sparkfun/SparkFun_RTK_EVK/docs/assets/board_files/dimensions.png

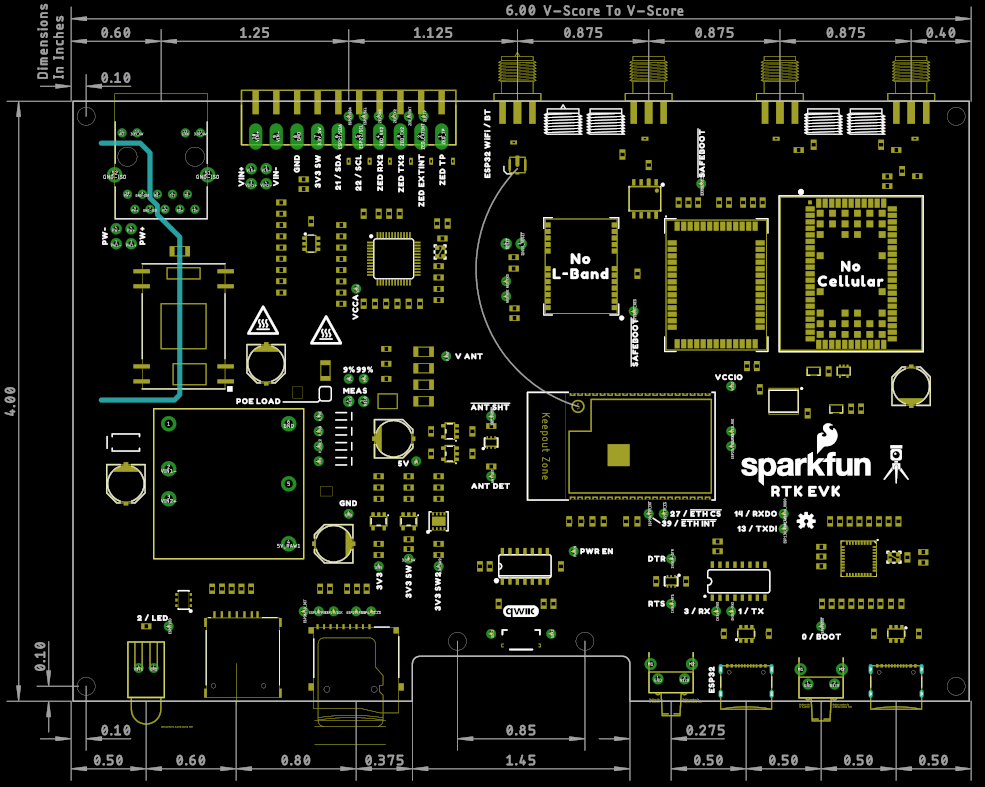
docs/assets/board_files/dimensions.png
