sparkfun/SparkFun_RTK_EVK/docs/assets/board_files/SparkFun_RTK_EVK-Back.png

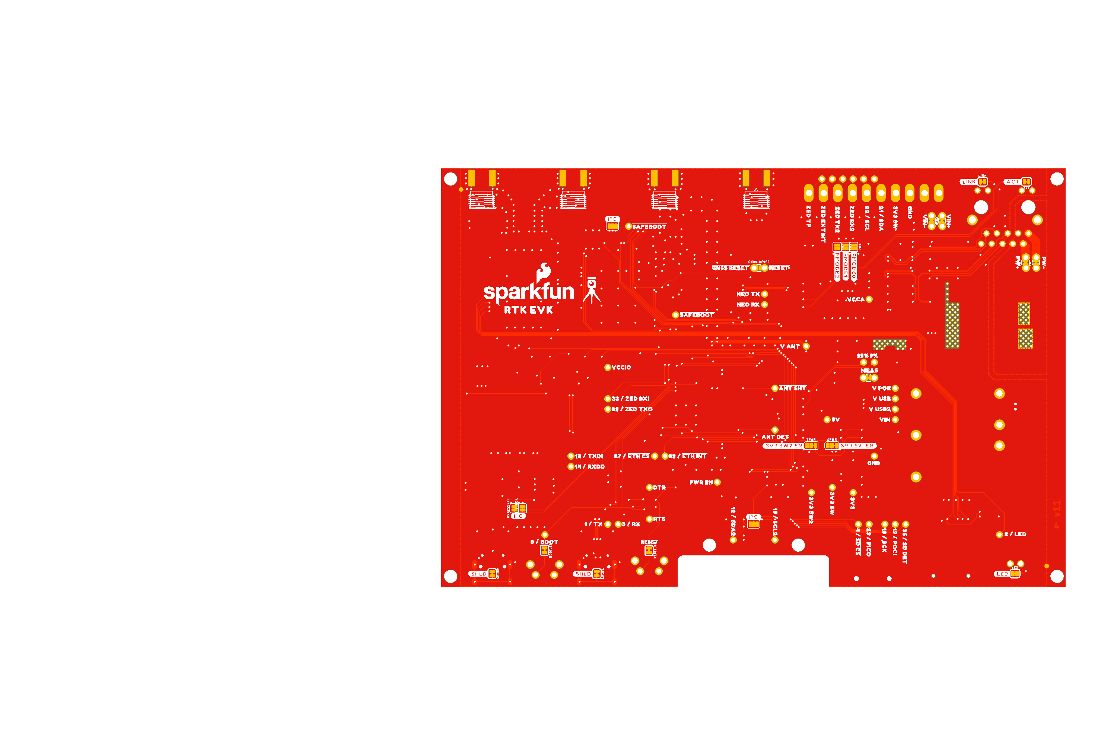
docs/assets/board_files/SparkFun_RTK_EVK-Back.png
