sparkfun/SparkFun_RTK_EVK/docs/assets/board_files/SparkFun_RTK_EVK.png

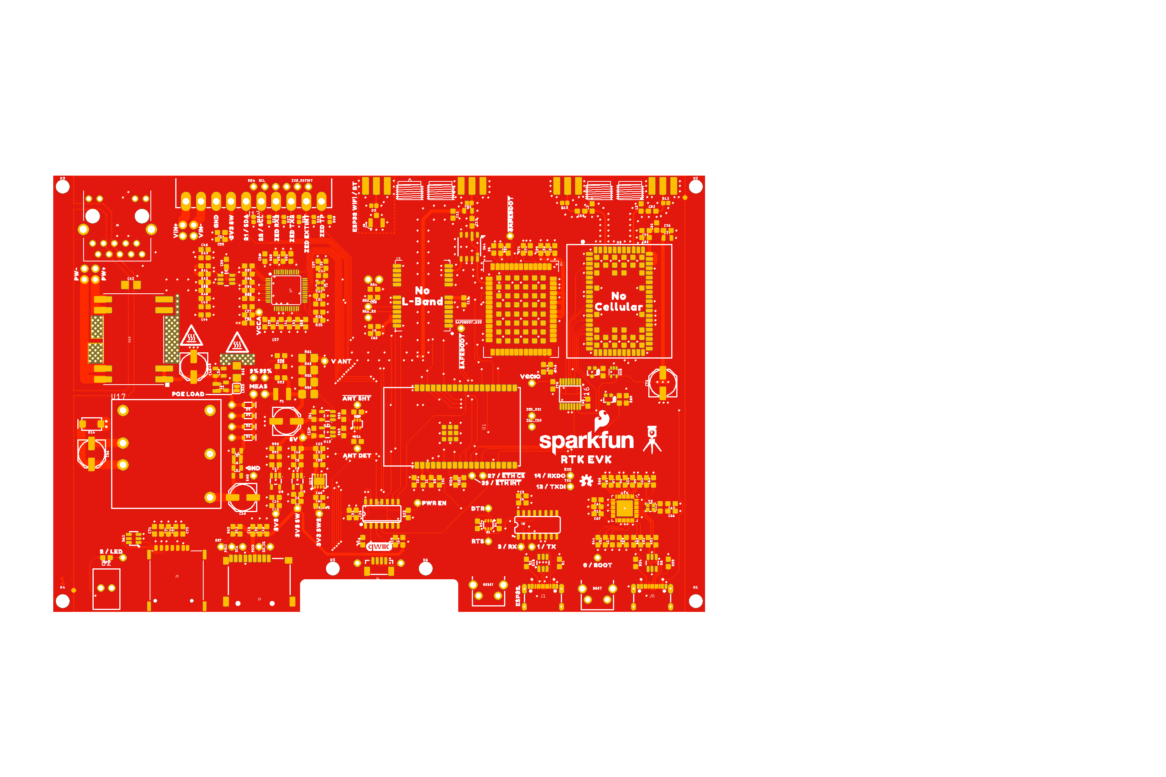
docs/assets/board_files/SparkFun_RTK_EVK.png
