sparkfun/SparkFun_RTK_EVK/docs/assets/img/24342-RTK-EVK-Feature.jpg

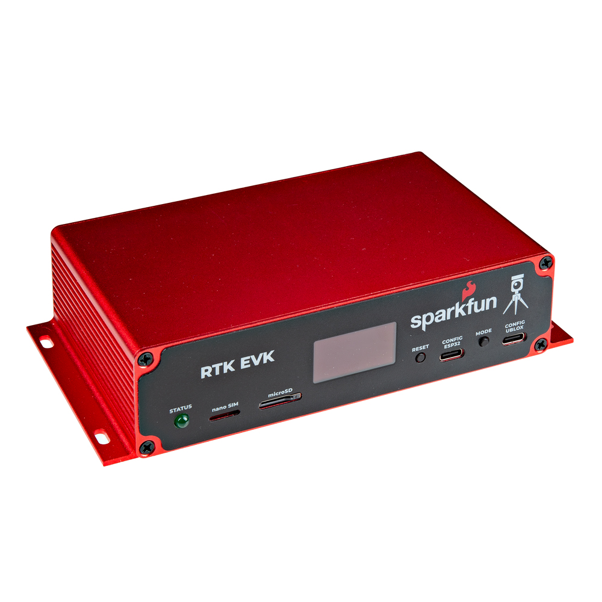
docs/assets/img/24342-RTK-EVK-Feature.jpg
