sparkfun/SparkFun_RTK_EVK/docs/assets/img/PCB.png

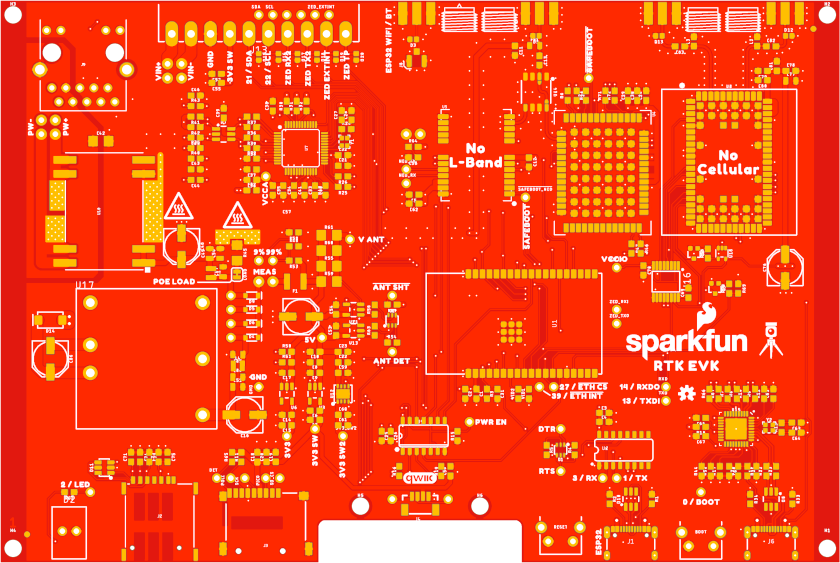
docs/assets/img/PCB.png
