sparkfun/SparkFun_RTK_EVK/docs/assets/RTK_EVK_Enclosure/Rear_Panel/RTK_EVK_Rear_Panel.pdf

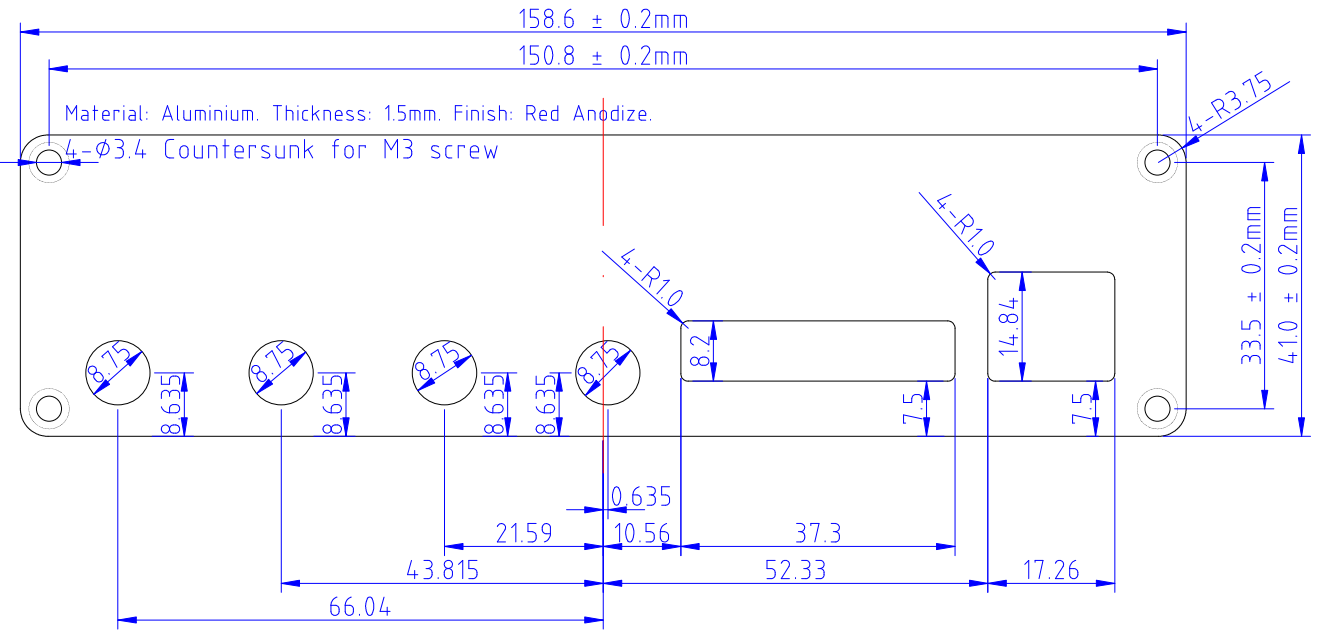
[picture p86: page 1]
