sparkfun/SparkFun_RTK_EVK/docs/assets/RTK_EVK_Enclosure/Rear_Sticker/RTK_EVK_Rear_Sticker_Dimensions.pdf

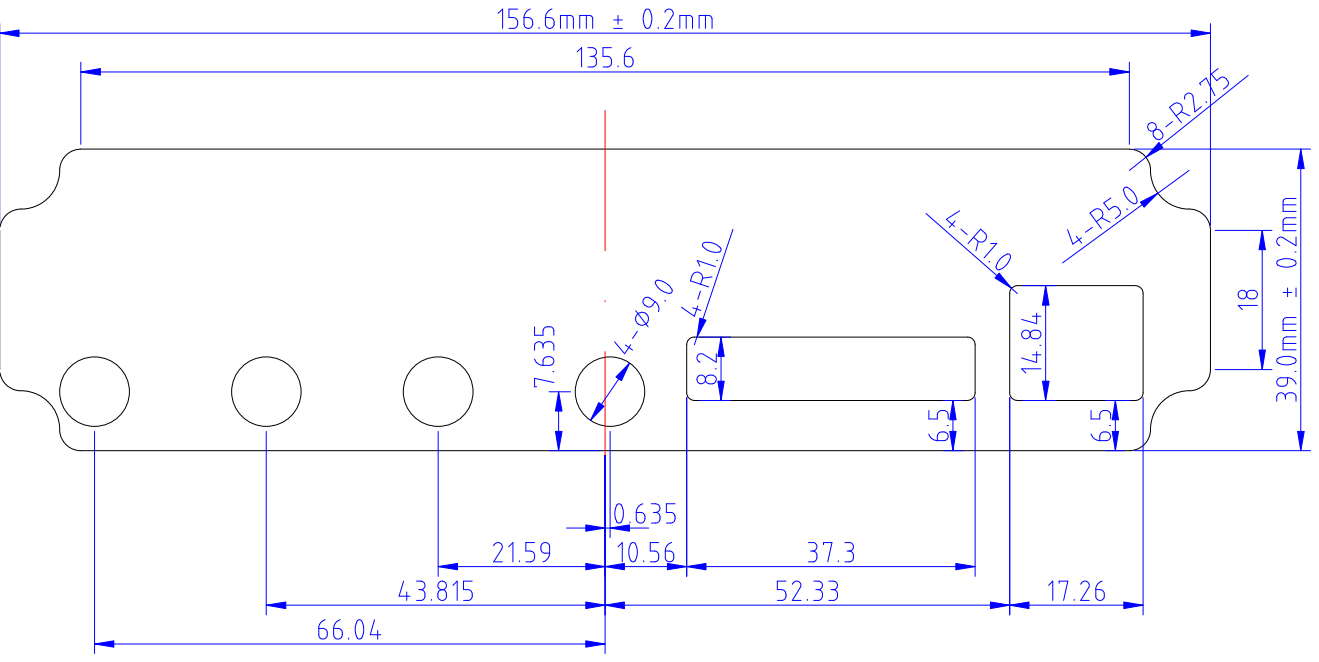
[picture p87: page 1]
