sparkfun/SparkFun_RTK_EVK/docs/assets/RTK_EVK_Enclosure/Front_Panel/RTK_EVK_Front_Panel.pdf

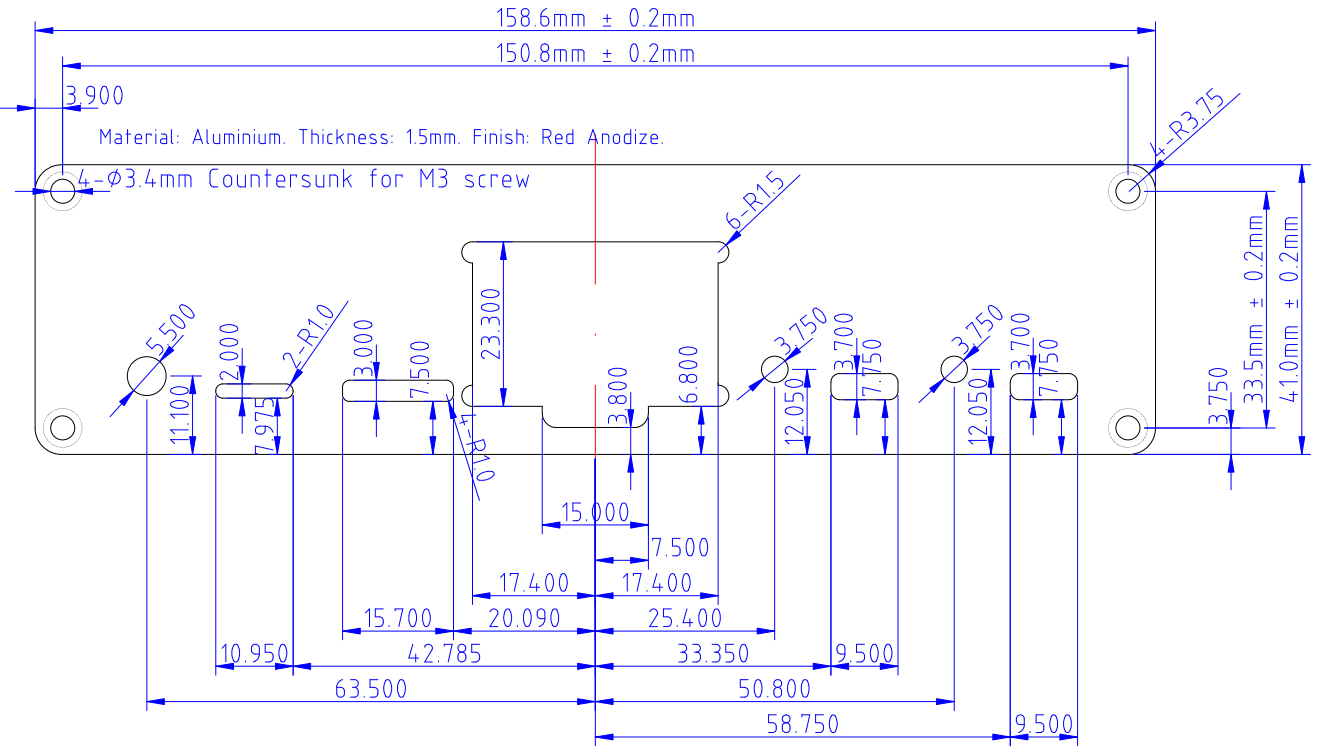
[picture p88: page 1]
