sparkfun/SparkFun_RTK_EVK/Example_Sketches/6_2_LBand_Corrections_with_NEO-D9S/6_2_LBand_Corrections_with_NEO-D9S.ino

/*
  SparkFun RTK EVK Test Sketch

  License: MIT. Please see LICENSE.md for more details

  This example shows how to receive u-blox PointPerfect L-Band correction data
  with the NEO-D9S and transfer it to the ZED-F9P over UART or I2C.

  The L-Band SPARTN correction data is encrypted; the ZED-F9P requires keys to decrypt it.
  Update secrets.h with your PointPerfect L-Band keys from Thingstream.

  ESP32-WROVER-IE Pin Allocations:
  D0  : Boot + Boot Button
  D1  : Serial TX (CH340 RX)
  D2  : STAT LED
  D3  : Serial RX (CH340 TX)
  D4  : SD CS
  D5  : GNSS Time Pulse - via 74HC4066 switch and PWREN
  D12 : SDA2 - Qwiic OLED - via 74HC4066 switch and PWREN
  D13 : Serial1 TX - LARA_TXDI
  D14 : Serial1 RX - LARA RXDO
  D15 : SCL2 - Qwiic OLED - via 74HC4066 switch and PWREN
  D16 : N/A
  D17 : N/A
  D18 : SPI SCK
  D19 : SPI POCI
  D21 : I2C SDA
  D22 : I2C SCL
  D23 : SPI PICO
  D25 : Serial2 RX - ZED-F9P TXO
  D26 : LARA Power On
  D27 : Ethernet Chip Select
  D32 : PWREN
  D33 : Serial2 TX - ZED-F9P RXI
  A34 : LARA Network Indicator
  A35 : Board Detect (3.0V)
  A36 : SD Card Detect
  A39 : Ethernet Interrupt
*/

#define noPush // Uncomment this line to disable pushing the correction data over I2C

#include "secrets.h" // <- Copy and paste the Current Key and Next Key into secrets.h

#include <Wire.h> // Needed for I2C to GNSS
TwoWire I2C_1 = TwoWire(0);

#include <SparkFun_u-blox_GNSS_v3.h> //http://librarymanager/All#SparkFun_u-blox_GNSS_v3
SFE_UBLOX_GNSS myGNSS; // ZED-F9x
SFE_UBLOX_GNSS myLBand; // NEO-D9S

const uint32_t myLBandFreq = 1556290000; // Uncomment this line to use the US SPARTN 1.8 service
//const uint32_t myLBandFreq = 1545260000; // Uncomment this line to use the EU SPARTN 1.8 service

#define OK(ok) (ok ? F("  ->  OK") : F("  ->  ERROR!")) // Convert uint8_t into OK/ERROR

const int STAT_LED = 2;
const int SD_CS = 4; // Chip select for the microSD card
const int GNSS_INT = 5; // ZED_F9P time pulse interrupt
const int SDA_2 = 12; // OLED
const int SERIAL1_TX = 13; // LARA_TXDI
const int SERIAL1_RX = 14; // LARA RXDO
const int SCL_2 = 15; // OLED
const int SDA_1 = 21; // ZED-F9P and NEO-D9S
const int SCL_1 = 22; // ZED-F9P and NEO-D9S
const int SERIAL2_RX = 25; // ZED-F9P TXO
const int LARA_PWR = 26; // LARA_PWR_ON - inverted - set LARA_PWR high to pull LARA_PWR_ON low
const int ETHERNET_CS = 27; // Chip select for the WizNet W5500
const int PWREN = 32; // 74HC4066 switch Enable - pull high to enable SCL2/SDA2 and GNSS_INT
const int SERIAL2_TX = 33; // ZED-F9P RXI
const int LARA_NI = 34; // LARA Network Indicator - only valid when the LARA is powered on
const int SD_PRESENT = 36; // microSD card card present - from the microSD socket switch
const int ETHERNET_INT = 39; // WizNet W5500 interrupt

//=-=-=-=-=-=-=-=-=-=-=-=-=-=-=-=-=-=-=-=-=-=-=-=-=-=-=-=-=-=-=-=-=-=-=-=-=-=-=-=-=-=-=-=-=

// Callback: pushRXMPMP will be called when new PMP data arrives
// See u-blox_structs.h for the full definition of UBX_RXM_PMP_message_data_t
//         _____  You can use any name you like for the callback. Use the same name when you call setRXMPMPmessageCallbackPtr
//        /               _____  This _must_ be UBX_RXM_PMP_message_data_t
//        |              /              _____ You can use any name you like for the struct
//        |              |             /
//        |              |             |
void pushRXMPMP(UBX_RXM_PMP_message_data_t *pmpData)
{
  //Extract the raw message payload length
  uint16_t payloadLen = ((uint16_t)pmpData->lengthMSB << 8) | (uint16_t)pmpData->lengthLSB;
  Serial.print(F("New RXM-PMP data received. Message payload length is "));
  Serial.print(payloadLen);

#ifndef noPush

  Serial.println(F(" Bytes. Pushing it to the GNSS..."));
  
  //Push the PMP data to the GNSS
  //The payload length could be variable, so we need to push the header and payload, then checksum
  myGNSS.pushRawData(&pmpData->sync1, (size_t)payloadLen + 6); // Push the sync chars, class, ID, length and payload
  myGNSS.pushRawData(&pmpData->checksumA, (size_t)2); // Push the checksum bytes

#else

  Serial.println(F(" Bytes."));

#endif

}

//=-=-=-=-=-=-=-=-=-=-=-=-=-=-=-=-=-=-=-=-=-=-=-=-=-=-=-=-=-=-=-=-=-=-=-=-=-=-=-=-=-=-=-=-=

// Callback: printPVTdata will be called when new NAV PVT data arrives
// See u-blox_structs.h for the full definition of UBX_NAV_PVT_data_t
//         _____  You can use any name you like for the callback. Use the same name when you call setAutoPVTcallbackPtr
//        /                  _____  This _must_ be UBX_NAV_PVT_data_t
//        |                 /               _____ You can use any name you like for the struct
//        |                 |              /
//        |                 |              |
void printPVTdata(UBX_NAV_PVT_data_t *ubxDataStruct)
{
  double latitude = ubxDataStruct->lat; // Print the latitude
  Serial.print(F("Lat: "));
  Serial.print(latitude / 10000000.0, 7);

  double longitude = ubxDataStruct->lon; // Print the longitude
  Serial.print(F("  Long: "));
  Serial.print(longitude / 10000000.0, 7);

  double altitude = ubxDataStruct->hMSL; // Print the height above mean sea level
  Serial.print(F("  Height: "));
  Serial.print(altitude / 1000.0, 3);

  uint8_t fixType = ubxDataStruct->fixType; // Print the fix type
  Serial.print(F("  Fix: "));
  Serial.print(fixType);
  if (fixType == 0)
    Serial.print(F(" (None)"));
  else if (fixType == 1)
    Serial.print(F(" (Dead Reckoning)"));
  else if (fixType == 2)
    Serial.print(F(" (2D)"));
  else if (fixType == 3)
    Serial.print(F(" (3D)"));
  else if (fixType == 3)
    Serial.print(F(" (GNSS + Dead Reckoning)"));
  else if (fixType == 5)
    Serial.print(F(" (Time Only)"));
  else
    Serial.print(F(" (UNKNOWN)"));

  uint8_t carrSoln = ubxDataStruct->flags.bits.carrSoln; // Print the carrier solution
  Serial.print(F("  Carrier Solution: "));
  Serial.print(carrSoln);
  if (carrSoln == 0)
    Serial.print(F(" (None)"));
  else if (carrSoln == 1)
    Serial.print(F(" (Floating)"));
  else if (carrSoln == 2)
    Serial.print(F(" (Fixed)"));
  else
    Serial.print(F(" (UNKNOWN)"));

  uint32_t hAcc = ubxDataStruct->hAcc; // Print the horizontal accuracy estimate
  Serial.print(F("  Horizontal Accuracy Estimate: "));
  Serial.print(hAcc);
  Serial.print(F(" (mm)"));

  Serial.println();    
}

//=-=-=-=-=-=-=-=-=-=-=-=-=-=-=-=-=-=-=-=-=-=-=-=-=-=-=-=-=-=-=-=-=-=-=-=-=-=-=-=-=-=-=-=-=

// Callback: printRXMCOR will be called when new RXM COR data arrives
// See u-blox_structs.h for the full definition of UBX_RXM_COR_data_t
//         _____  You can use any name you like for the callback. Use the same name when you call setRXMCORcallbackPtr
//        /                  _____  This _must_ be UBX_RXM_COR_data_t
//        |                 /               _____ You can use any name you like for the struct
//        |                 |              /
//        |                 |              |
void printRXMCOR(UBX_RXM_COR_data_t *ubxDataStruct)
{
  Serial.print(F("UBX-RXM-COR:  ebno: "));
  Serial.print((double)ubxDataStruct->ebno / 8, 3); //Convert ebno to dB

  Serial.print(F("  protocol: "));
  if (ubxDataStruct->statusInfo.bits.protocol == 1)
    Serial.print(F("RTCM3"));
  else if (ubxDataStruct->statusInfo.bits.protocol == 2)
    Serial.print(F("SPARTN"));
  else if (ubxDataStruct->statusInfo.bits.protocol == 29)
    Serial.print(F("PMP (SPARTN)"));
  else if (ubxDataStruct->statusInfo.bits.protocol == 30)
    Serial.print(F("QZSSL6"));
  else
    Serial.print(F("Unknown"));

  Serial.print(F("  errStatus: "));
  if (ubxDataStruct->statusInfo.bits.errStatus == 1)
    Serial.print(F("Error-free"));
  else if (ubxDataStruct->statusInfo.bits.errStatus == 2)
    Serial.print(F("Erroneous"));
  else
    Serial.print(F("Unknown"));

  Serial.print(F("  msgUsed: "));
  if (ubxDataStruct->statusInfo.bits.msgUsed == 1)
    Serial.print(F("Not used"));
  else if (ubxDataStruct->statusInfo.bits.msgUsed == 2)
    Serial.print(F("Used"));
  else
    Serial.print(F("Unknown"));

  Serial.print(F("  msgEncrypted: "));
  if (ubxDataStruct->statusInfo.bits.msgEncrypted == 1)
    Serial.print(F("Not encrypted"));
  else if (ubxDataStruct->statusInfo.bits.msgEncrypted == 2)
    Serial.print(F("Encrypted"));
  else
    Serial.print(F("Unknown"));

  Serial.print(F("  msgDecrypted: "));
  if (ubxDataStruct->statusInfo.bits.msgDecrypted == 1)
    Serial.print(F("Not decrypted"));
  else if (ubxDataStruct->statusInfo.bits.msgDecrypted == 2)
    Serial.print(F("Successfully decrypted"));
  else
    Serial.print(F("Unknown"));

  Serial.println();
}

//=-=-=-=-=-=-=-=-=-=-=-=-=-=-=-=-=-=-=-=-=-=-=-=-=-=-=-=-=-=-=-=-=-=-=-=-=-=-=-=-=-=-=-=-=

void setup()
{
  pinMode(SD_CS, OUTPUT);
  digitalWrite(SD_CS, HIGH);
  pinMode(ETHERNET_CS, OUTPUT);
  digitalWrite(ETHERNET_CS, HIGH);
  pinMode(PWREN, OUTPUT);
  digitalWrite(PWREN, HIGH);

  delay(1000);

  Serial.begin(115200);
  Serial.println("SparkFun RTK EVK - Test Sketch");

  I2C_1.begin((int)SDA_1, (int)SCL_1, (uint32_t)400000); // Start I2C

  //=-=-=-=-=-=-=-=-=-=-=-=-=-=-=-=-=-=-=-=-=-=-=-=-=-=-=-=-=-=-=-=-=-=-=-=-=-=-=-=-=-=-=-=-=
  // Begin and configure the ZED-F9x

  //myGNSS.enableDebugging(); // Uncomment this line to enable helpful debug messages on Serial

  while (myGNSS.begin(I2C_1) == false) //Connect to the u-blox module using Wire port
  {
    Serial.println(F("u-blox GNSS module not detected at default I2C address. Please check wiring."));
    delay(2000);
  }
  Serial.println(F("u-blox GNSS module connected"));

  uint8_t ok = myGNSS.setI2COutput(COM_TYPE_UBX); //Turn off NMEA noise
  if (ok) ok = myGNSS.setI2CInput(COM_TYPE_UBX | COM_TYPE_NMEA | COM_TYPE_SPARTN); //Be sure SPARTN input is enabled
  if (ok) ok = myGNSS.setUART1Input(COM_TYPE_UBX | COM_TYPE_NMEA | COM_TYPE_SPARTN); //Be sure SPARTN input is enabled
  if (ok) ok = myGNSS.setDGNSSConfiguration(SFE_UBLOX_DGNSS_MODE_FIXED); // Set the differential mode - ambiguities are fixed whenever possible
  if (ok) ok = myGNSS.setNavigationFrequency(1); //Set output in Hz.
  if (ok) ok = myGNSS.setVal8(UBLOX_CFG_SPARTN_USE_SOURCE, 1); // use LBAND PMP message
  if (ok) ok = myGNSS.setVal8(UBLOX_CFG_MSGOUT_UBX_RXM_COR_I2C, 1); // Enable UBX-RXM-COR messages on I2C
  
  //Configure the SPARTN IP Dynamic Keys
  //"When the receiver boots, the host should send 'current' and 'next' keys in one message." - Use setDynamicSPARTNKeys for this.
  //"Every time the 'current' key is expired, 'next' takes its place."
  //"Therefore the host should then retrieve the new 'next' key and send only that." - Use setDynamicSPARTNKey for this.
  // The key can be provided in binary (uint8_t) format or in ASCII Hex (char) format, but in both cases keyLengthBytes _must_ represent the binary key length in bytes.
  if (ok) ok = myGNSS.setDynamicSPARTNKeys(currentKeyLengthBytes, currentKeyGPSWeek, currentKeyGPSToW, currentDynamicKey,
                                           nextKeyLengthBytes, nextKeyGPSWeek, nextKeyGPSToW, nextDynamicKey);

  //if (ok) ok = myGNSS.saveConfiguration(VAL_CFG_SUBSEC_IOPORT | VAL_CFG_SUBSEC_MSGCONF); //Optional: Save the ioPort and message settings to NVM and BBR
  
  Serial.print(F("GNSS: configuration "));
  Serial.println(OK(ok));

  myGNSS.setAutoPVTcallbackPtr(&printPVTdata); // Enable automatic NAV PVT messages with callback to printPVTdata so we can watch the carrier solution go to fixed

  myGNSS.setRXMCORcallbackPtr(&printRXMCOR); // Print the contents of UBX-RXM-COR messages so we can check if the PMP data is being decrypted successfully

  //=-=-=-=-=-=-=-=-=-=-=-=-=-=-=-=-=-=-=-=-=-=-=-=-=-=-=-=-=-=-=-=-=-=-=-=-=-=-=-=-=-=-=-=-=
  // Begin and configure the NEO-D9S L-Band receiver

  //myLBand.enableDebugging(); // Uncomment this line to enable helpful debug messages on Serial

  while (myLBand.begin(I2C_1, 0x43) == false) //Connect to the u-blox NEO-D9S using Wire port. The D9S default I2C address is 0x43 (not 0x42)
  {
    Serial.println(F("u-blox NEO-D9S not detected at default I2C address. Please check wiring."));
    delay(2000);
  }
  Serial.println(F("u-blox NEO-D9S connected"));

  myLBand.newCfgValset(); // Create a new Configuration Interface message - this defaults to VAL_LAYER_RAM_BBR (change in RAM and BBR)
  myLBand.addCfgValset(UBLOX_CFG_PMP_CENTER_FREQUENCY,     myLBandFreq); // Default 1539812500 Hz
  myLBand.addCfgValset(UBLOX_CFG_PMP_SEARCH_WINDOW,        2200);        // Default 2200 Hz
  myLBand.addCfgValset(UBLOX_CFG_PMP_USE_SERVICE_ID,       0);           // Default 1 
  myLBand.addCfgValset(UBLOX_CFG_PMP_SERVICE_ID,           21845);       // Default 50821
  myLBand.addCfgValset(UBLOX_CFG_PMP_DATA_RATE,            2400);        // Default 2400 bps
  myLBand.addCfgValset(UBLOX_CFG_PMP_USE_DESCRAMBLER,      1);           // Default 1
  myLBand.addCfgValset(UBLOX_CFG_PMP_DESCRAMBLER_INIT,     26969);       // Default 23560
  myLBand.addCfgValset(UBLOX_CFG_PMP_USE_PRESCRAMBLING,    0);           // Default 0
  myLBand.addCfgValset(UBLOX_CFG_PMP_UNIQUE_WORD,          16238547128276412563ull); 
  myLBand.addCfgValset(UBLOX_CFG_MSGOUT_UBX_RXM_PMP_I2C,   1);           // Ensure UBX-RXM-PMP is enabled on the I2C port 
  myLBand.addCfgValset(UBLOX_CFG_MSGOUT_UBX_RXM_PMP_UART1, 1);           // Output UBX-RXM-PMP on UART1
  myLBand.addCfgValset(UBLOX_CFG_UART1_BAUDRATE,           38400);       // match baudrate with ZED default
  ok = myLBand.sendCfgValset(); // Apply the settings
  
  Serial.print(F("L-Band: configuration "));
  Serial.println(OK(ok));

  myLBand.softwareResetGNSSOnly(); // Do a restart

  myLBand.setRXMPMPmessageCallbackPtr(&pushRXMPMP); // Call pushRXMPMP when new PMP data arrives. Push it to the GNSS
}

//=-=-=-=-=-=-=-=-=-=-=-=-=-=-=-=-=-=-=-=-=-=-=-=-=-=-=-=-=-=-=-=-=-=-=-=-=-=-=-=-=-=-=-=-=

void loop()
{
  myGNSS.checkUblox(); // Check for the arrival of new GNSS data and process it.
  myGNSS.checkCallbacks(); // Check if any GNSS callbacks are waiting to be processed.

  myLBand.checkUblox(); // Check for the arrival of new PMP data and process it.
  myLBand.checkCallbacks(); // Check if any LBand callbacks are waiting to be processed.
}
