sparkfun/SparkFun_RTK_EVK/Example_Sketches/4_13_Multiple_WiFi_Users/secrets.h

// List the fixed ESP-NOW peers
const uint8_t espNowPeer[][6] =
{
};
const int espNowPeerCount = sizeof(espNowPeer) / sizeof(espNowPeer[0][6]);

const char * mdnsHostName = "Your_Host_Name";

const char * wifiSSID1 = "Your_WiFi_SSID";
const char * wifiPassword1 = "Your_WiFi_Password";
const char * wifiSSID2 = "Second_WiFi_SSID";
const char * wifiPassword2 = "Second_WiFi_Password";
const char * wifiSSID3 = "Third_WiFi_SSID";
const char * wifiPassword3 = "Third_WiFi_Password";
const char * wifiSSID4 = "Fourth_WiFi_SSID";
const char * wifiPassword4 = "Fourth_WiFi_Password";

const char * wifiApSsid = "Your_Soft_AP_SSID";
const char * wifiApPassword = "Your_Soft_AP_Password";
