sparkfun/SparkFun_RTK_EVK/Example_Sketches/4_11_WiFi_AP_Setup/secrets.h

const char * hostName = "EVK";

const char * wifiApSSID = "Soft-AP";
const char * wifiApPassword = "Password";

const char * apIpAddress = nullptr;
const char * apSubnetMask = nullptr;
const char * apGatewayAddress = nullptr;
const char * apDnsAddress = nullptr;
const char * apDhcpFirstAddress = nullptr;
