sparkfun/SparkFun_RTK_EVK/Example_Sketches/9_5_PPP_HTTPS/Network.ino

//----------------------------------------
// Process network events

std::vector<arduino_event_id_t> eventQueue; // vector of network events

void networkOnEvent(arduino_event_id_t event, arduino_event_info_t info)
{
    IPAddress ipv4;

    switch (event)
    {
    default:
        if (event != ARDUINO_EVENT_PPP_GOT_IP6)
            Serial.printf("ERROR: Unknown Arduino event: %d\r\n", event);
        break;

    case ARDUINO_EVENT_PPP_START:
    case ARDUINO_EVENT_PPP_CONNECTED:
    case ARDUINO_EVENT_PPP_GOT_IP:
    case ARDUINO_EVENT_PPP_LOST_IP:
    case ARDUINO_EVENT_PPP_DISCONNECTED:
    case ARDUINO_EVENT_PPP_STOP:
        if (USE_EVENT_QUEUE)
            eventQueue.push_back(event);
        else
            pppEvent(event);
        break;
    }
}

void processEventQueue()
{
    if (USE_EVENT_QUEUE)
    {
        auto it = eventQueue.begin();
        if (it != eventQueue.end())
        {
            pppEvent(*it);
            eventQueue.erase(it);
        }
    }
}
