sparkfun/SparkFun_RTK_EVK/Example_Sketches/9_5_PPP_HTTPS/Cert_AWS.h

//----------------------------------------
// AWS certificate for PointPerfect API
// CN=Amazon Root CA 1,O=Amazon,C=US   PEM
// See: https://www.amazontrust.com/repository/
const char * caAmazonWebServices = R"=====(
-----BEGIN CERTIFICATE-----
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
rqXRfboQnoZsG4q5WTP468SQvvG5
-----END CERTIFICATE-----
)=====";
