sparkfun/SparkFun_RTK_EVK/Example_Sketches/8_6_PointPerfect_MQTT_WiFi_ETH_Cellular/secrets.h

static const char WIFI_SSID[] = "<ADD YOUR WIFI SSID HERE>";
static const char WIFI_PASSWORD[] = "<ADD YOUR WIFI PASSWORD HERE>";

static const char POINTPERFECT_TOKEN[] = "<ADD YOUR POINTPERFECT TOKEN HERE>"; // "ABCDABCD-ABCD-ABCD-ABCD-ABCDABCDABCD"
static const char ZTP_HARDWARE_ID[] = "<ADD YOUR 14 CHARACTER HARDWARE ID HERE>";  // "ABCDABCDABCD00"
static const char ZTP_GIVEN_NAME[] = "<ADD YOUR FULL THING NAME HERE>"; // "EVK d99.99 - ABCDABCDABCD00"

// Amazon Root Certificate
static const char AWS_CERT_CA[] PROGMEM = R"EOF(-----BEGIN CERTIFICATE-----
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
rqXRfboQnoZsG4q5WTP468SQvvG5
-----END CERTIFICATE-----)EOF";
