sparkfun/SparkFun_RTK_EVK/Example_Sketches/6_2_LBand_Corrections_with_NEO-D9S/secrets.h

// You can set the information below after signing up with the u-blox Thingstream portal 
// and adding a new New PointPerfect Thing (L-Band or L-Band + IP)
// https://portal.thingstream.io/app/location-services/things
// In the new PointPerfect Thing, you go to the credentials tab and copy and paste the IP Dynamic Keys here.
//
// The keys are valid from a particular GPS Week Number and Time of Week.
// Looking at the credentials tab, the current key expires 23:59 Feb 11th 2022.
// This means the next key is valid _from_ Midnight Feb 12th 2022.
// That is GPS Week 2196. The GPS Time of Week in seconds is 518400.
// Working backwards, the current key became valid exactly 4 weeks earlier (Midnight Jan 15th 2022).
//
// See: https://www.labsat.co.uk/index.php/en/gps-time-calculator
//
// The keys are given as: 32 hexadecimal digits = 128 bits = 16 Bytes
//
// The next example shows how to retrieve the keys using ESP32 WiFi and MQTT.
// You can cut and paste the keys and GPS week/time-of-week from that example into here.

const uint8_t currentKeyLengthBytes =   16; 
const char currentDynamicKey[] =        "<ADD YOUR L-Band or L-Band + IP DYNAMIC KEY HERE>";
const uint16_t currentKeyGPSWeek =      2297; // Update this when you add new keys
const uint32_t currentKeyGPSToW =       86400;

const uint8_t nextKeyLengthBytes =      16; 
const char nextDynamicKey[] =           "<ADD YOUR L-Band or L-Band + IP DYNAMIC KEY HERE>";
const uint16_t nextKeyGPSWeek =         2301; // Update this when you add new keys
const uint32_t nextKeyGPSToW =          86400;
